ageppert/Core16-Interactive-Core-Memory/Datasheets/LED REV MOUNT Sample LED.jpeg

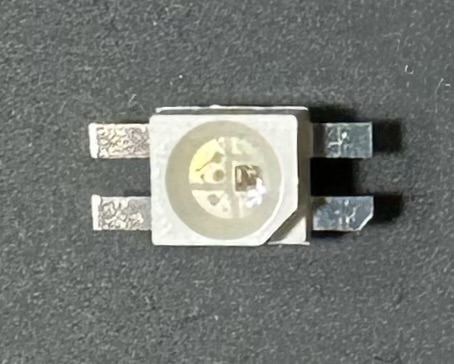
Datasheets/LED REV MOUNT Sample LED.jpeg
