ageppert/Core16-Interactive-Core-Memory/Datasheets/LED REV MOUNT SK6812 light side in PCB.png

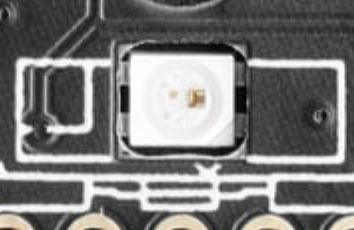
Datasheets/LED REV MOUNT SK6812 light side in PCB.png
