ageppert/Core16-Interactive-Core-Memory/Manufacturing Assembly/Core16 Weave Pattern.png

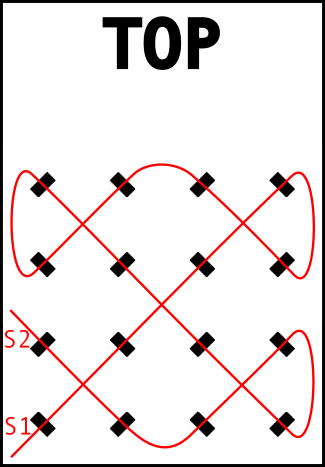
Manufacturing Assembly/Core16 Weave Pattern.png
